giltesa/Nintendo-GameCube-USB-C-Kit/2. Renders, 3D models/Cap/Game Cube USB-C v33.png

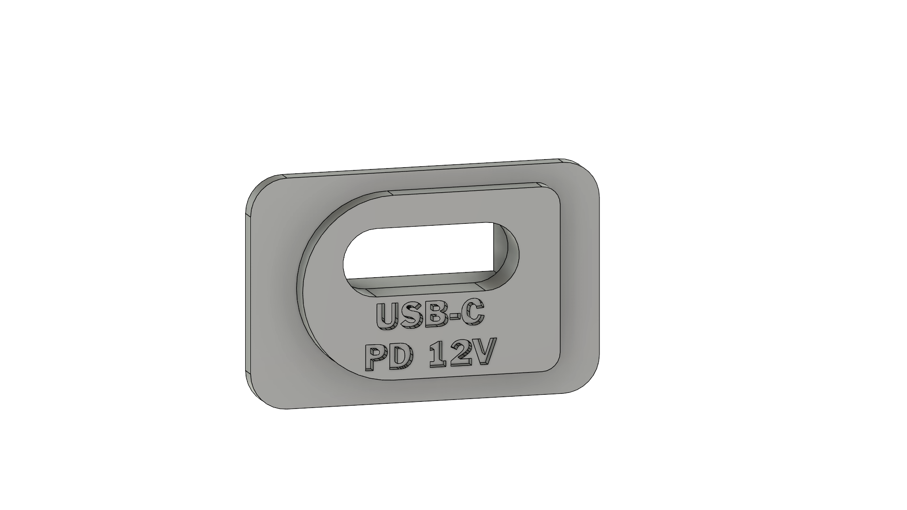
2. Renders, 3D models/Cap/Game Cube USB-C v33.png
