giltesa/Nintendo-GameCube-USB-C-Kit/2. Renders, 3D models/Game Cube USB-C v1.1.png

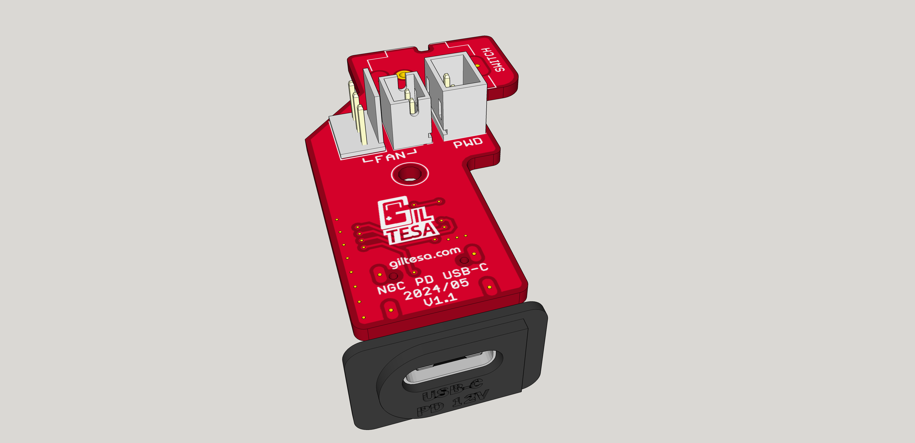
2. Renders, 3D models/Game Cube USB-C v1.1.png
